m-gracia/esp32-bike-computer-back/include/my_def.h

#ifndef _MY_DEF_H_
#define _MY_DEF_H_
#include <Arduino.h>

// Bluetooth
#include <BLEDevice.h>
#include <BLEUtils.h>
#include <BLEScan.h>
#include <BLEAdvertisedDevice.h>
#include <BLERemoteCharacteristic.h>
#include <BLEAddress.h>
#define BTSCANTIME 5
#define BT_GENERIC_DISPLAY 320
#define BT_VEHICLE_MOTORBIKE 2244
#define BT_DEVICE_NAME "Jarvis-back"     // BLE device name
static const BLEUUID MOTORBIKE_SERVICE_UUID = BLEUUID("cb99fdf2-bebe-cafe-b1bf-bf9803b2df01");
static const BLEUUID DISTANCE_CHARACTERISTIC_UUID = BLEUUID("cb99fdf2-bebe-cafe-b1bf-bf9803b2df01");    //Distance
extern BLEAdvertisedDevice* myDevice;
extern BLEClient*  pClient;
extern BLERemoteService* pRemoteService;
extern BLERemoteCharacteristic* pCharDistance;
extern BLEScan* pBLEScan;

// ToF VL53L0X sensor
#include "Adafruit_VL53L0X.h"
#define I2C_SDA 9
#define I2C_SCL 10
// VL53L0X configuration. Choose only one
// #define TOF_SENSE Adafruit_VL53L0X::VL53L0X_SENSE_DEFAULT
// #define TOF_SENSE Adafruit_VL53L0X::VL53L0X_SENSE_LONG_RANGE
// #define TOF_SENSE Adafruit_VL53L0X::VL53L0X_SENSE_HIGH_SPEED
#define TOF_SENSE Adafruit_VL53L0X::VL53L0X_SENSE_HIGH_ACCURACY
#define TOF_PERIOD 200 // Measure period (ms)
static Adafruit_VL53L0X tofDev = Adafruit_VL53L0X();

// Distance marks for showing bars
static unsigned char distanceMark = 100;    // Detected mark
static unsigned char distanceMark1 = 40;    // Closest mark
static unsigned char distanceMark2 = 60;    // Close mark
static unsigned char distanceMark3 = 80;    // Far mark
static unsigned char distanceMark4 = 100;   // Farthest mark

//Status IDs
#define STATUS_UNK 8        // Unknown
#define STATUS_CRIT 2       // Critical
#define STATUS_WARN 1       // Warning
#define STATUS_OK 0         // OK

//Status variables
extern unsigned char bikeBT;        // Bluetooth Status
extern unsigned char bikeDistance;  // Distance Status

/* To show changes on LCD's
 *
 * The bits are set when a new information needs to be updated on the LCD's
 * 1 - GPS Speed (Not used here)
 * 2 - GPRS Status (Not used here)
 * 3 - TPMS Front (Not used here)
 * 4 - TPMS Rear (Not used here)
 * 5 - GPS Heigh (Not used here)
 * 6 - Hour,minute (Not used here)
 * 7 - Date (Not used here)
 * 8 - CPU status (Not used here)
 * 9 - GPS Status (Not used here)
 * 10 - Phone battery (Not used here)
 * 11 - Street name (Not used here)
 * 12 - Speed limit (Not used here)
 * 13 - GPS Satellites (Not used here)
 * 14 - City and weather (Not used here)
 * 15 - USonic distance
 */
extern unsigned long bikeDataChanged;

// Run timers
extern unsigned long timerBT;
extern unsigned long timerDistance;

// Task
extern TaskHandle_t T_loopOthers;

#endif  // _MY_DEF_H_
