m-gracia/esp32-bike-computer-back/include/bluetooth.h

#ifndef _BLUETOOTH_H_
#define _BLUETOOTH_H_

void initBT();      // Initialize Bluetooth
void connectBT();   // Connect to main ESP32
bool sendBT();     // Send data to main ESP32

#endif  // _BLUETOOTH_H_
